extsui/GardeningBoard/PRG/Tools/BuildingPainter/3_仮配置2.png

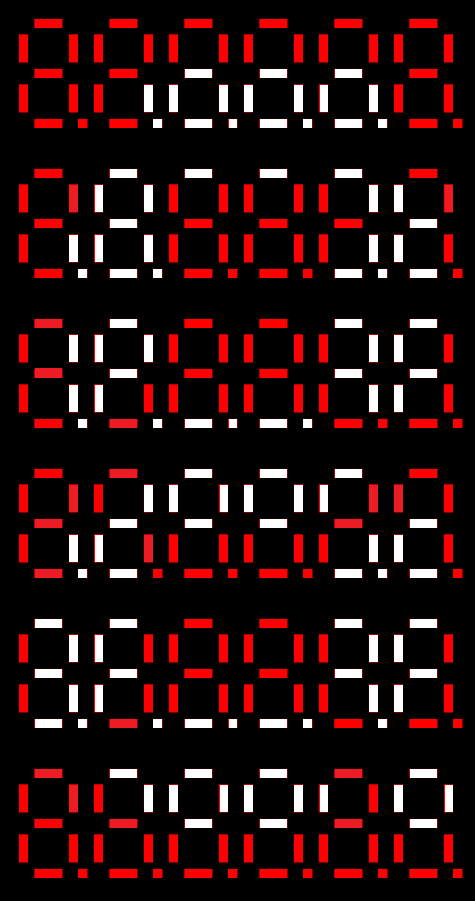
PRG/Tools/BuildingPainter/3_仮配置2.png
