extsui/GardeningBoard/PRG/Seeeduino/Pillar/IPillarState.h

#ifndef IPILLAR_STATE_H
#define IPILLAR_STATE_H

#include "PillarInput.h"
#include "PillarOutput.h"

////////////////////////////////////////////////////////////////////////////////
//  全体の状態制御関連
////////////////////////////////////////////////////////////////////////////////
enum class PillarMode {
    Idle = 0,   // 待機中
    BadApple,   // BadApple 再生中
    Script,     // スクリプト実行中
};

class IPillarState
{
public:
    virtual void OnEnter(PillarInput *pInput, PillarOutput *pOutput) = 0;
    virtual PillarMode OnExecute(PillarInput *pInput, PillarOutput *pOutput) = 0;
    virtual void OnExit(PillarInput *pInput, PillarOutput *pOutput) = 0;
};

#endif /* IPILLAR_STATE_H */
