extsui/GardeningBoard/PRG/Seeeduino/Pillar/PumpUtil.cpp

#include "PumpUtil.h"
#include <cstdint>
#include <cassert>
#include <cstddef>
#include <string.h>

#if CONFIG_XIAO
#include <Wire.h>
#endif

//////////////////////////////////////////////////////////////////////
//  プラットフォーム非依存
//////////////////////////////////////////////////////////////////////
/**
 * 16 進表記の 2 文字を 1 バイトに変換する。
 * 成功した場合は outValue に変換後の値が代入される。
 * @return 0: 成功 / -1: 失敗
 */
int PumpUtil::ToHex(uint8_t *outValue, char hi, char lo)
{
    uint8_t h, l;

    assert(outValue != NULL);
    
    if (('a' <= hi) && (hi <= 'f')) {
        h = hi - 'a' + 10;
    } else if (('A' <= hi) && (hi <= 'F')) {
        h = hi - 'A' + 10;
    } else if (('0' <= hi) && (hi <= '9')) {
        h = hi - '0';
    } else {
        return -1;
    }
    
    if (('a' <= lo) && (lo <= 'f')) {
        l = lo - 'a' + 10;
    } else if (('A' <= lo) && (lo <= 'F')) {
        l = lo - 'A' + 10;
    } else if (('0' <= lo) && (lo <= '9')) {
        l = lo - '0';
    } else {
        return -1;
    }
    
    *outValue = (h << 4) | (l & 0x0F);
    return 0;
}

/**
 * 生データ送信コマンドを解析する。
 * @param [in] command 入力文字列
 * @param [out] array 解析結果を格納する配列
 * @param [in] arrayLength 配列の長さ
 * @return 成功: 解釈できたバイト数 / 失敗: -1
 * 
 * 例: "@send xxaabbccdd.." (16 進数表記固定、xx はアドレス、データは可変長)
 */
int PumpUtil::ParseRawSendCommand(const char *command, uint8_t *array, int arrayLength)
{
    int result = 0;
    const char *prefix = "@send ";
    const int prefixLength = strlen(prefix);

    assert(command != NULL);
    assert(array != NULL);
    if (strncmp(&command[0], prefix, prefixLength) != 0) {
        return -1;
    }

    // arrayLength を越えるか command が最後まで到達したら終了
    int readPos = prefixLength;
    int writePos = 0;
    while ((writePos < arrayLength) && (command[readPos] != '\0')) {
        result = ToHex(&array[writePos], command[readPos], command[readPos + 1]);
        if (result == -1) {
            return -1;
        }
        readPos += 2;
        writePos++;
    }

    return writePos;
}

/**
 * 10 進数にした時の文字列長
 */
int PumpUtil::GetDigitLength(uint8_t value)
{
    if (value < 10) {
        return 1;
    } else if (value < 100) {
        return 2;
    } else {
        return 3;
    }
}

//////////////////////////////////////////////////////////////////////
//  XAIO 依存
//////////////////////////////////////////////////////////////////////

#if CONFIG_XIAO
/**
 * I2C データ送信トランザクション
 * @param [in] data データ列
 * - data[0]            : I2C アドレス
 * - data[1 ~ length-1] : I2C 送信データ
 * @param [in] length データサイズ
 * @return Wire.endTransmission() の戻り値をそのまま流用
 * - 0 : 成功
 * - 1 : データが長すぎて送信バッファに収まらない
 * - 2 : アドレスの送信時に受信されたNACK
 * - 3 : データの送信時に受信されたNACK
 * - 4 : その他のエラー
 */
int PumpUtil::WireTransaction(const uint8_t *data, int length)
{
    assert(data != NULL);
    Wire.beginTransmission(data[0]);
    if (length >= 1) {
        Wire.write(&data[1], length - 1);
    }
    return Wire.endTransmission();
}

#endif
